austinscreations/smart-usb-hub/version 2/design 1/schematic layout.jpg

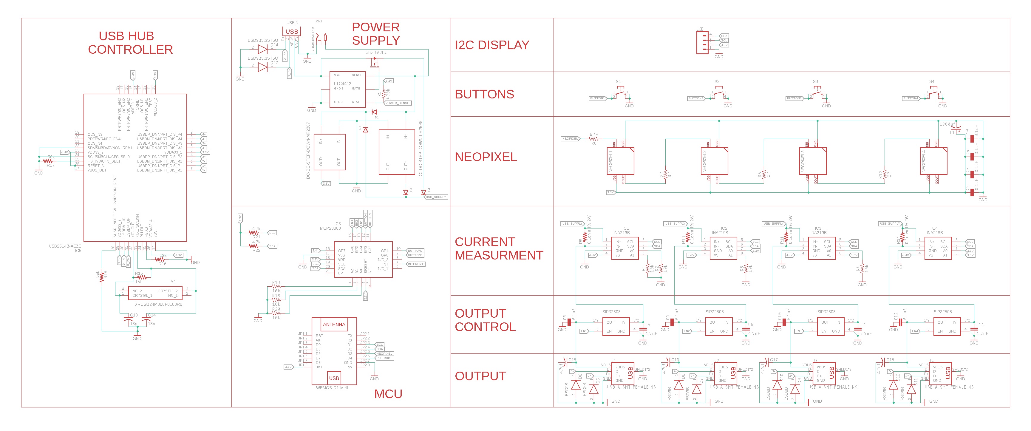
version 2/design 1/schematic layout.jpg
