austinscreations/smart-usb-hub/version 2/design 2/code/Node-Red Flows/Smart USB Hub mqtt.png

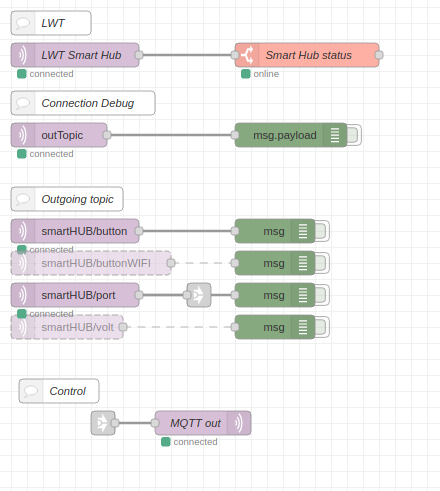
version 2/design 2/code/Node-Red Flows/Smart USB Hub mqtt.png
