austinscreations/smart-usb-hub/version 2/design 2/cross section/side b cross section case 1.png

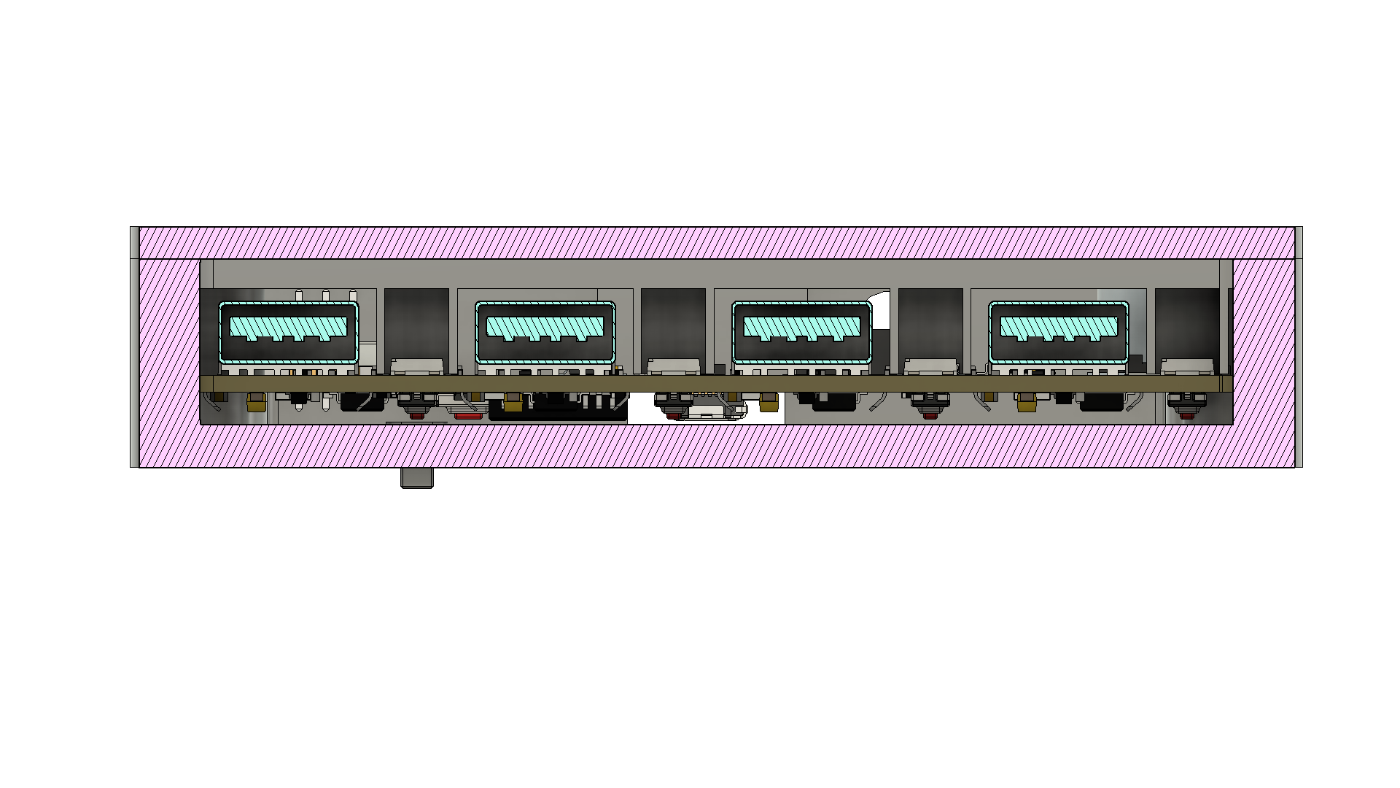
version 2/design 2/cross section/side b cross section case 1.png
