austinscreations/smart-usb-hub/version 2/design 2/PCB.png

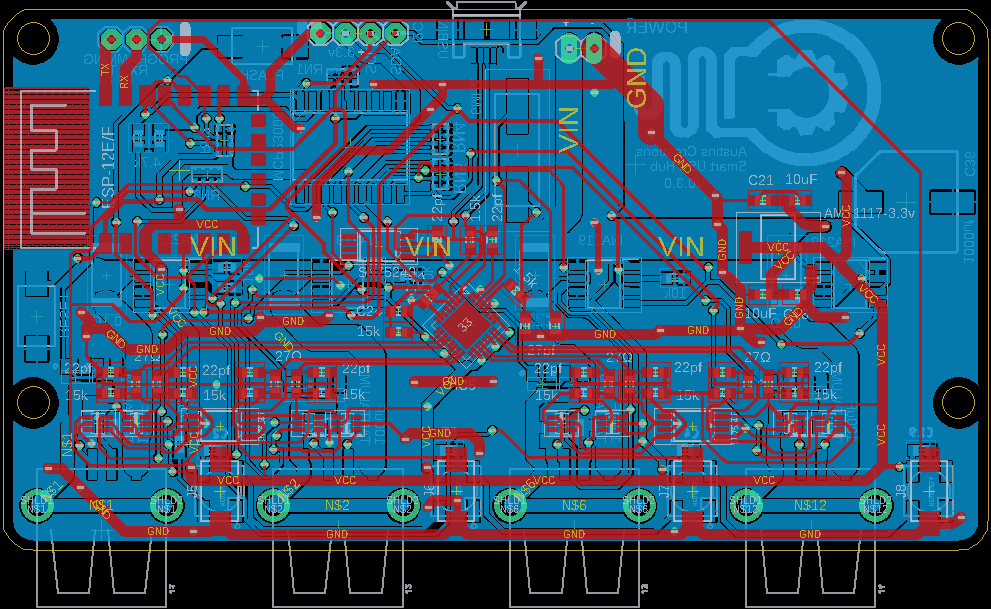
version 2/design 2/PCB.png
