austinscreations/smart-usb-hub/version 2/design 2/schematic.png

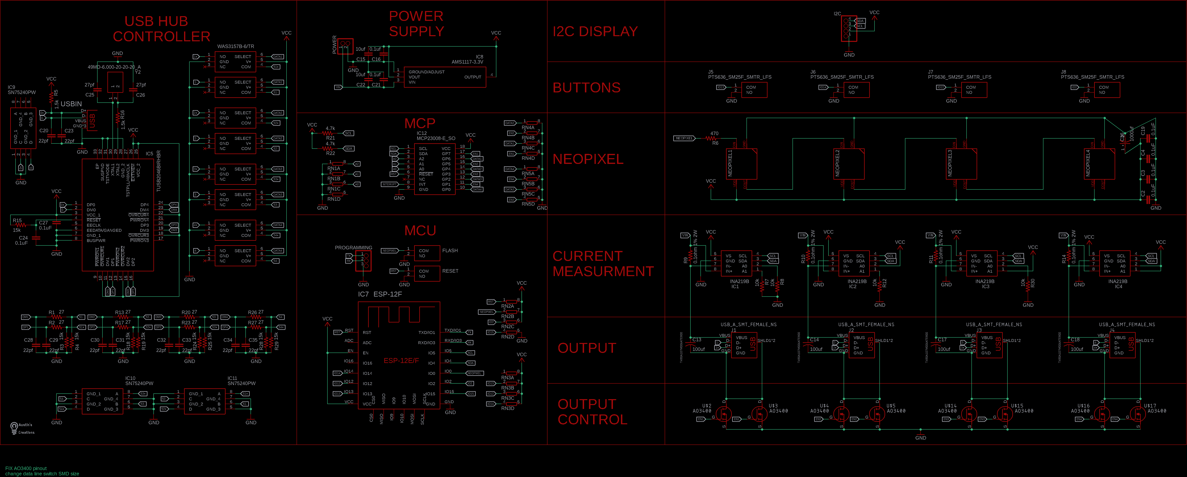
version 2/design 2/schematic.png
