austinscreations/smart-usb-hub/version 2/design 2/smart hub case v2 v25.png

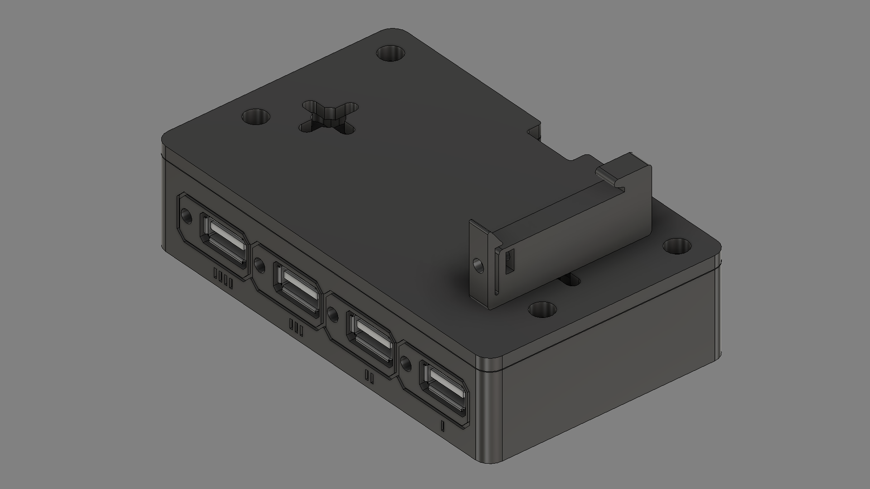
version 2/design 2/smart hub case v2 v25.png
