austinscreations/smart-usb-hub/version 2/design 2/Smart Hub PCB top.png

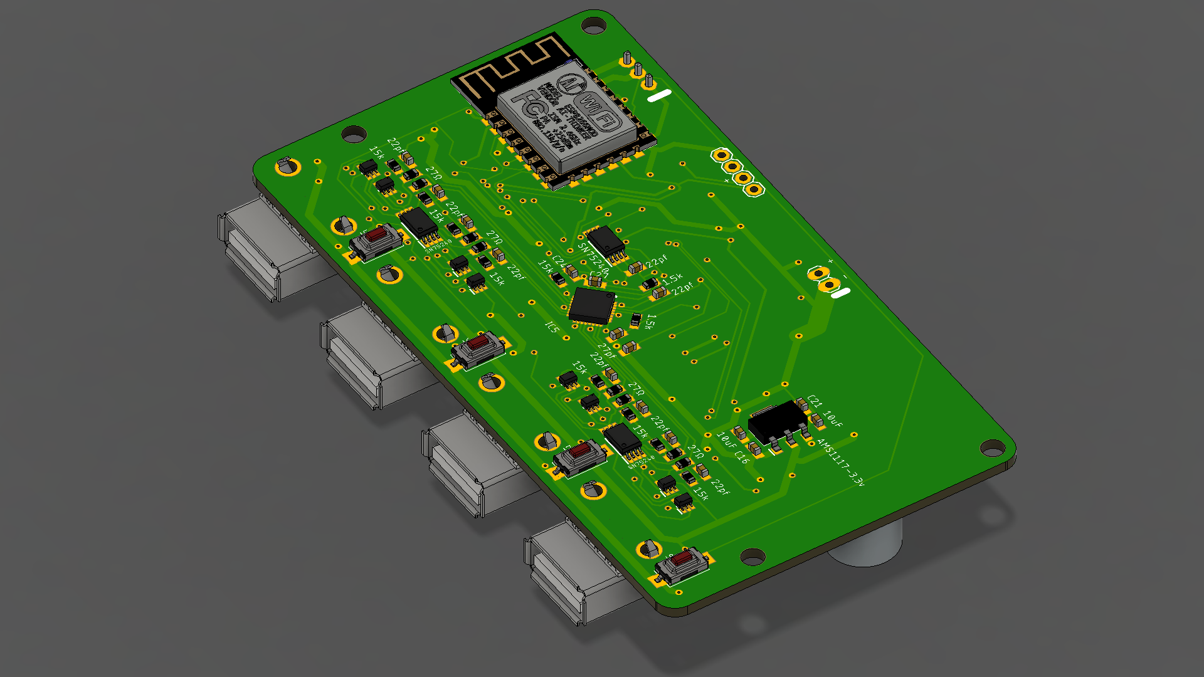
version 2/design 2/Smart Hub PCB top.png
