austinscreations/smart-usb-hub/version 2/design 2/v1/new front design.png

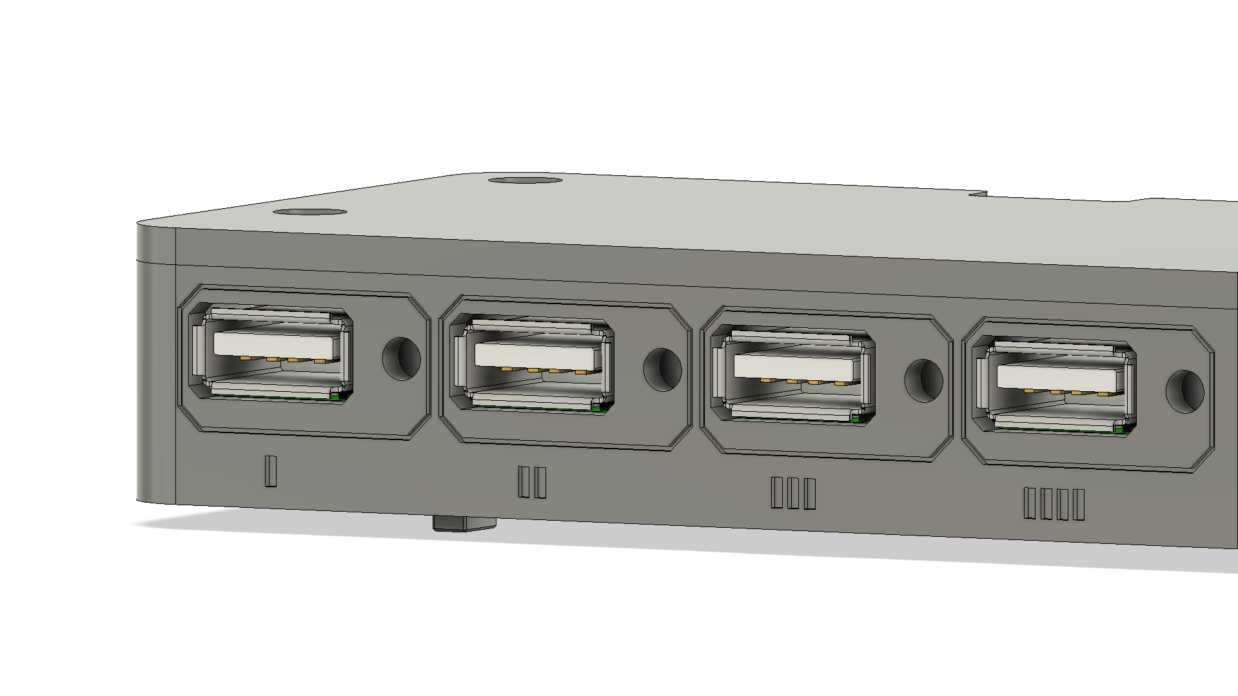
version 2/design 2/v1/new front design.png
