austinscreations/smart-usb-hub/version 2/design 2/v1/Smart Hub PCB bottom.png

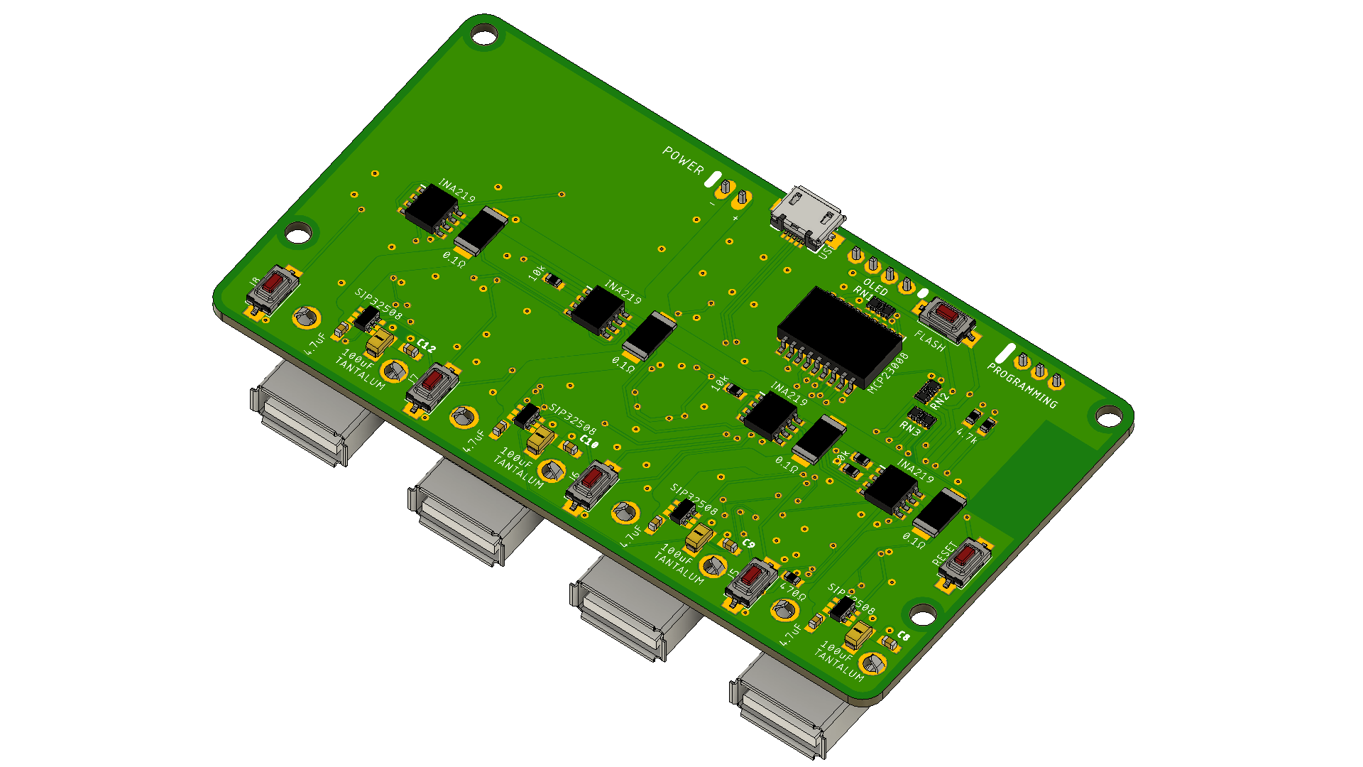
version 2/design 2/v1/Smart Hub PCB bottom.png
