austinscreations/smart-usb-hub/version 2/design 2/code/Node-Red Flows/Smart USB Hub manual.png

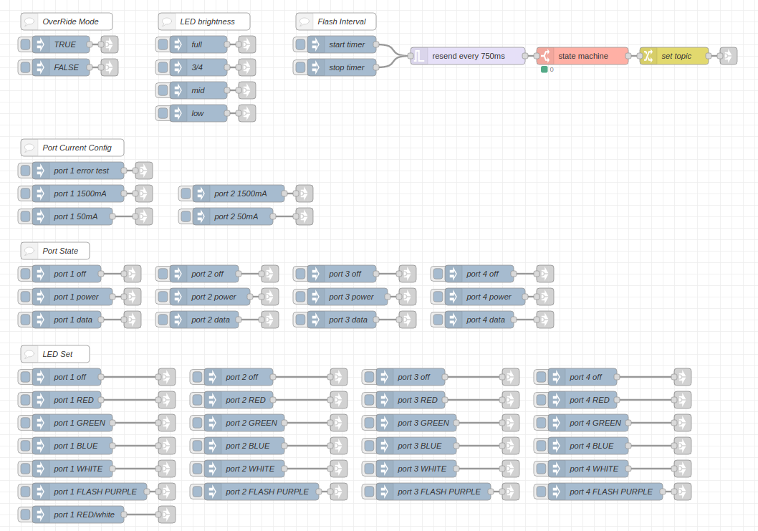
version 2/design 2/code/Node-Red Flows/Smart USB Hub manual.png
